cristianoag/retrolink/images/2026-09-20_19-45_1.png

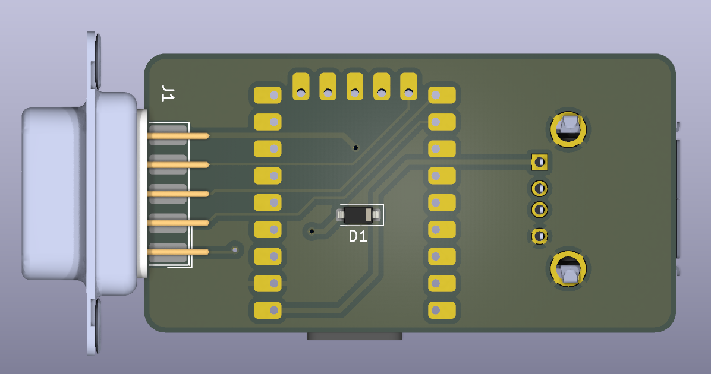
images/2026-09-20_19-45_1.png
