cristianoag/retrolink/software/usb/joystick/src/tusb_config.h

#ifndef RETROLINK_TUSB_CONFIG_H
#define RETROLINK_TUSB_CONFIG_H

#include "retrolink/board_config.h"

#ifndef CFG_TUSB_MCU
#define CFG_TUSB_MCU OPT_MCU_RP2040
#endif

#ifndef CFG_TUSB_OS
#define CFG_TUSB_OS OPT_OS_PICO
#endif
#define CFG_TUSB_DEBUG 0

#define CFG_TUD_ENABLED 1
#define CFG_TUH_ENABLED 1

#define BOARD_TUH_RHPORT 1
#define BOARD_TUH_RHPORT_SPEED OPT_MODE_FULL_SPEED

#ifndef CFG_TUH_RPI_PIO_USB
#define CFG_TUH_RPI_PIO_USB 1
#endif

#define CFG_TUH_RPI_PIO_USB_DP_PIN RETROLINK_USB_HOST_DP_GPIO

#define CFG_TUH_ENUMERATION_BUFSIZE 256
#define CFG_TUH_DEVICE_MAX 4
#define CFG_TUH_HUB 1
#define CFG_TUH_HID 4

#define CFG_TUH_ENDPOINT_MAX 8
#define CFG_TUH_INTERFACE_MAX 8
#define CFG_TUH_HID_EPIN_BUFSIZE 64
#define CFG_TUH_HID_EPOUT_BUFSIZE 64

#ifndef CFG_TUD_ENDPOINT0_SIZE
#define CFG_TUD_ENDPOINT0_SIZE 64
#endif

#define CFG_TUD_CDC 1
#define CFG_TUD_CDC_RX_BUFSIZE 256
#define CFG_TUD_CDC_TX_BUFSIZE 256
#define CFG_TUD_CDC_EP_BUFSIZE 64

#define CFG_TUSB_MEM_SECTION
#define CFG_TUSB_MEM_ALIGN __attribute__((aligned(4)))

#endif
